CNES/argos-demo-board/Public/Image/ARGOS DEMO N°2.png

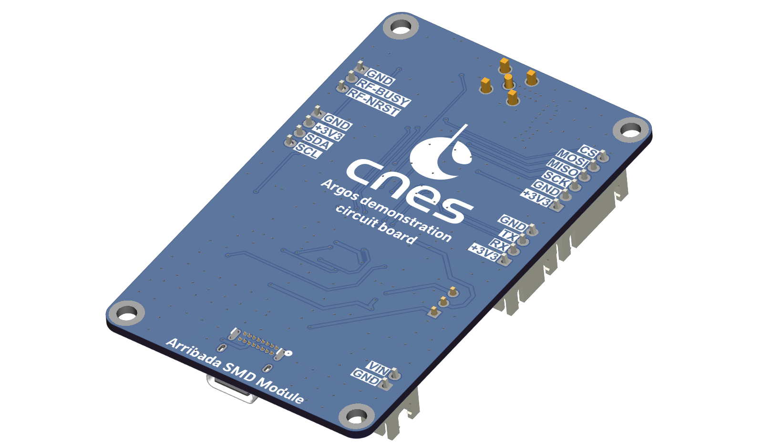
Public/Image/ARGOS DEMO N°2.png
