CNES/argos-demo-board/Public/Image/ARGOS DEMO N°7.png

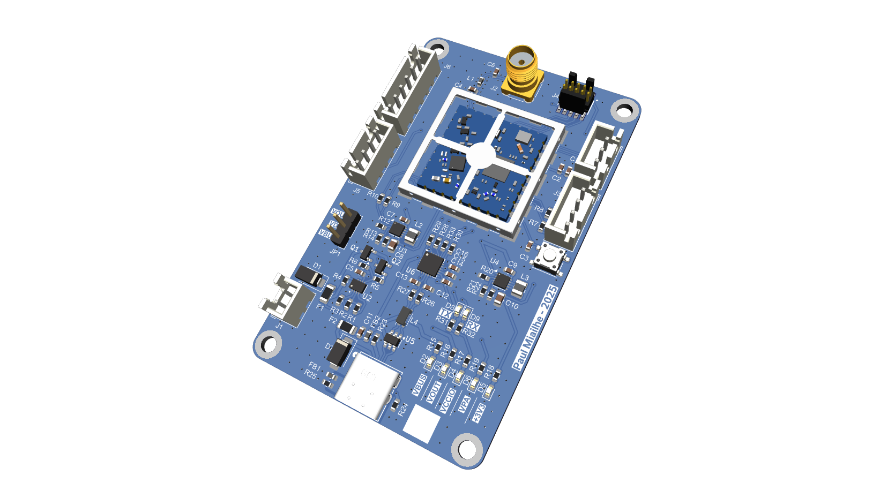
Public/Image/ARGOS DEMO N°7.png
