CNES/argos-demo-board/Public/Image/ARGOS DEMO N°11.png

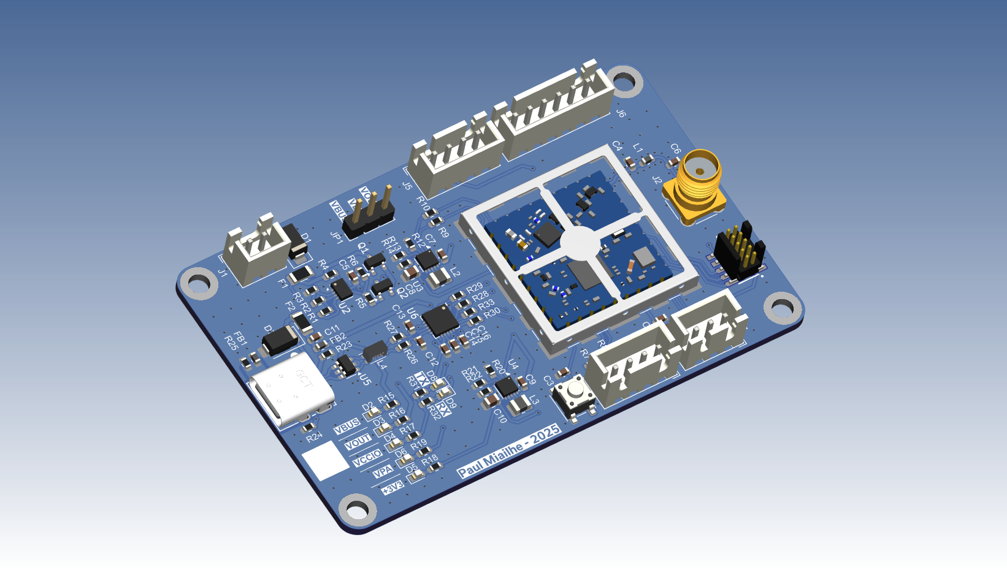
Public/Image/ARGOS DEMO N°11.png
