CNES/argos-demo-board/Public/Image/ARGOS DEMO N°12.png

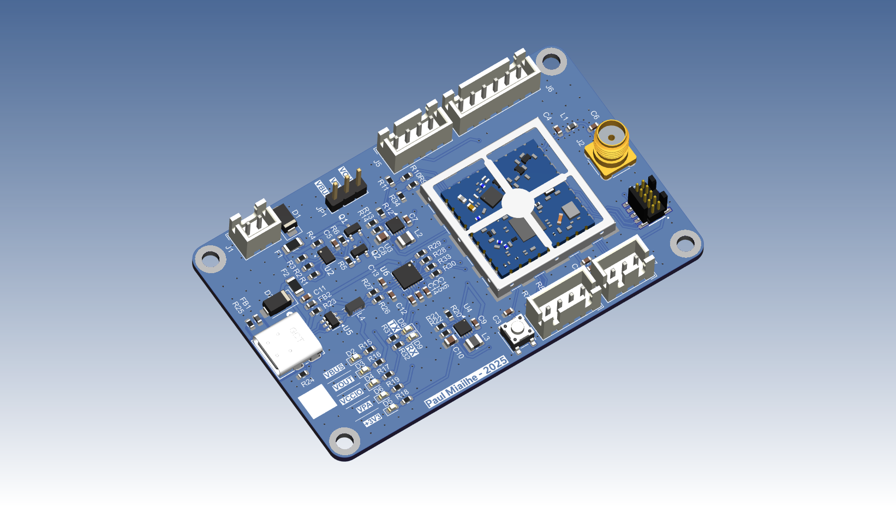
Public/Image/ARGOS DEMO N°12.png
