CNES/argos-demo-board/Public/Image/ARGOS DEMO N°14.png

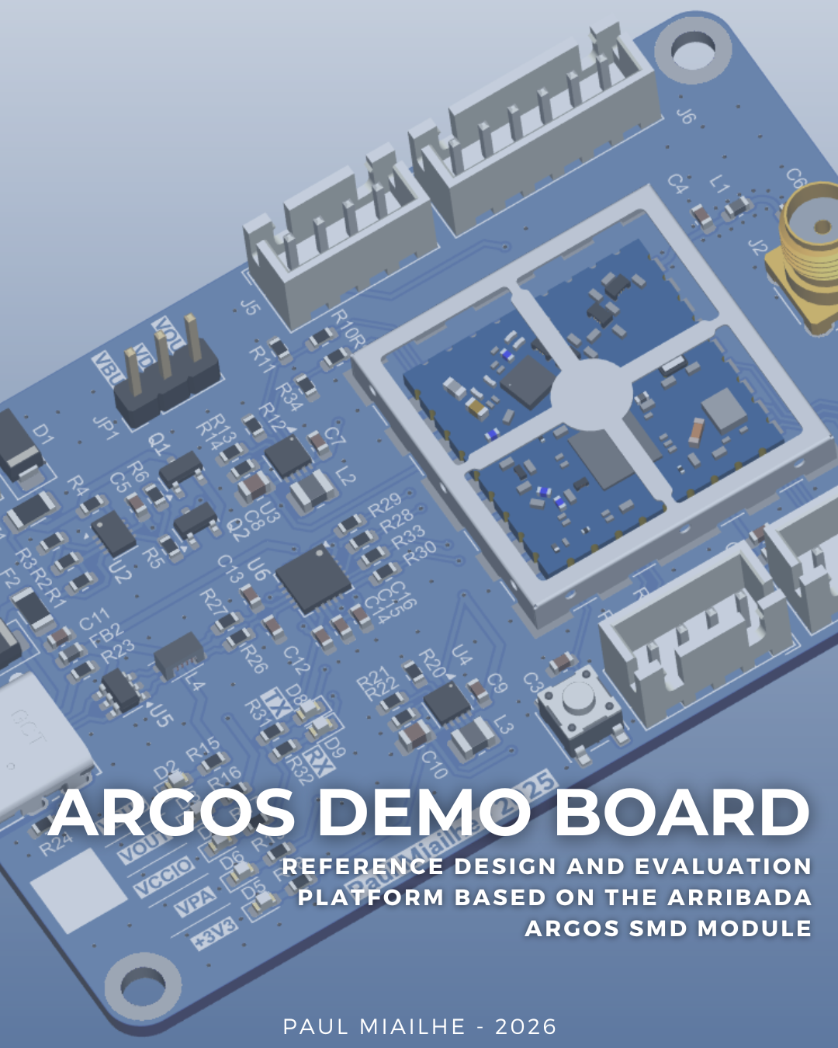
Public/Image/ARGOS DEMO N°14.png
