CNES/argos-demo-board/Librairies/3dmodels/FJ-15-D-02.00-4.stp

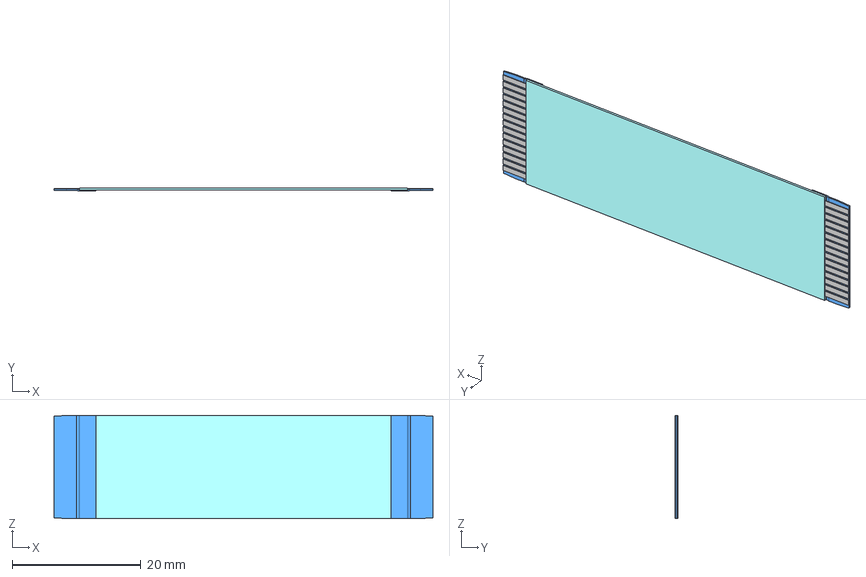
[picture p37: CAD file, 2026-01-29]
Librairies/3dmodels/FJ-15-D-02.00-4.stp
58.8 x 0.533 x 16.0 mm
FJ-15-D-02.00-4_cable
FJ-15-4_strip x 2
