CNES/argos-demo-board/Document/Test-VLDA4/Measurement037.png

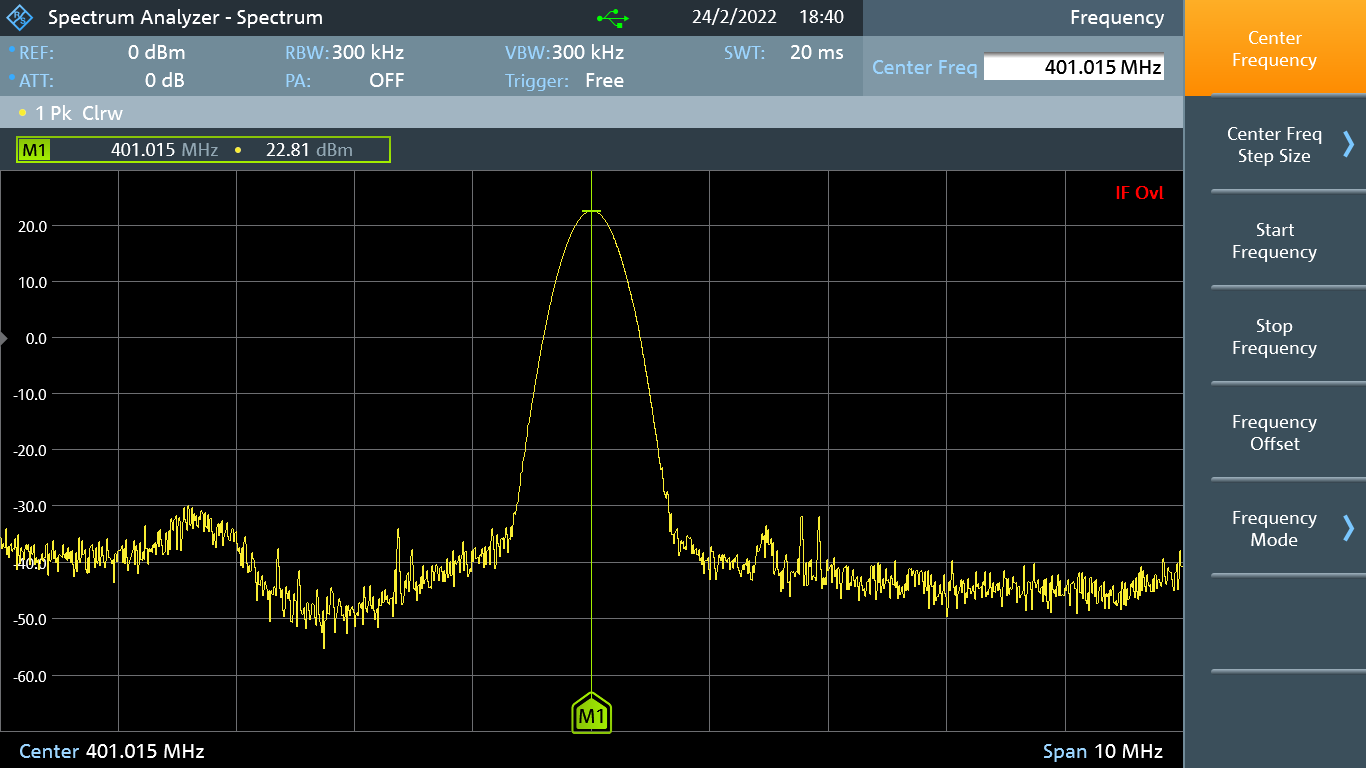
Document/Test-VLDA4/Measurement037.png
