CNES/argos-demo-board/Document/Test-VLDA4/Measurement038.png

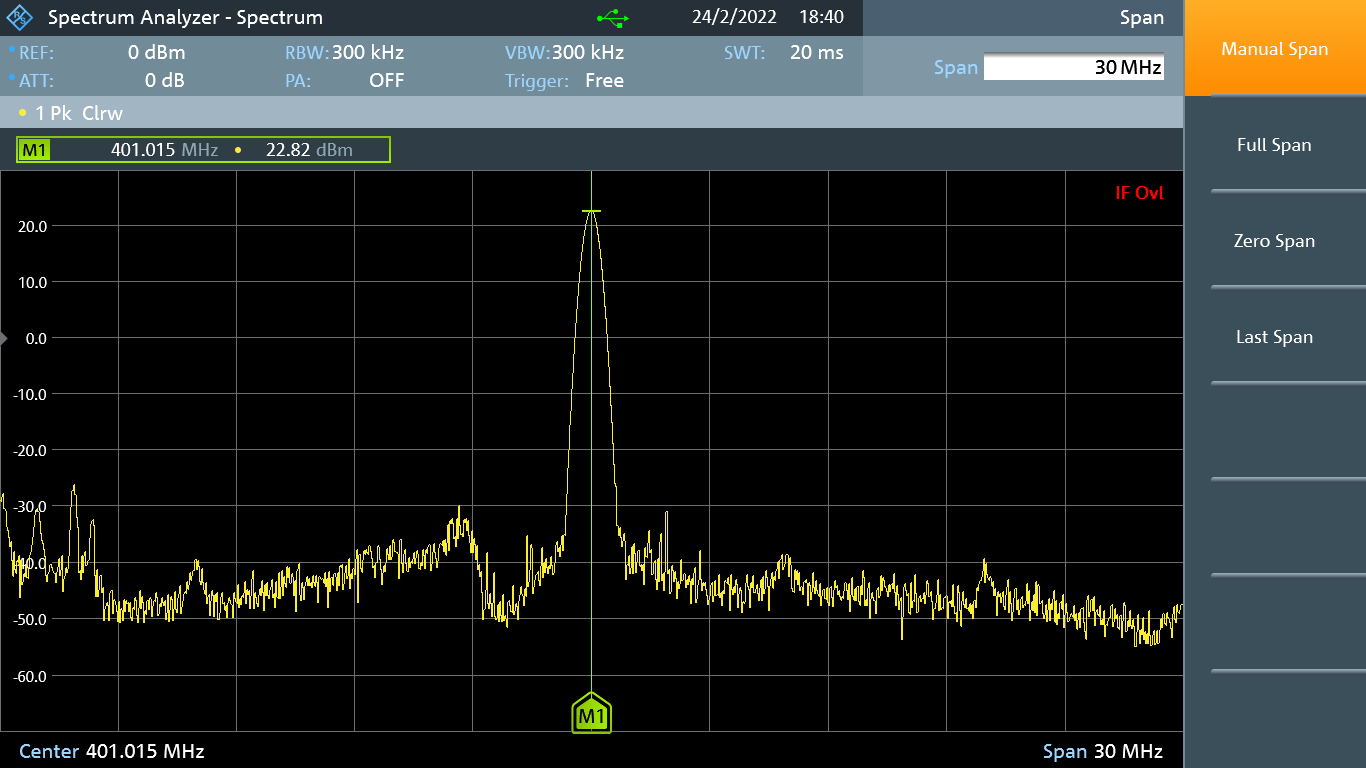
Document/Test-VLDA4/Measurement038.png
