CNES/argos-demo-board/Document/Test-VLDA4/Measurement040.png

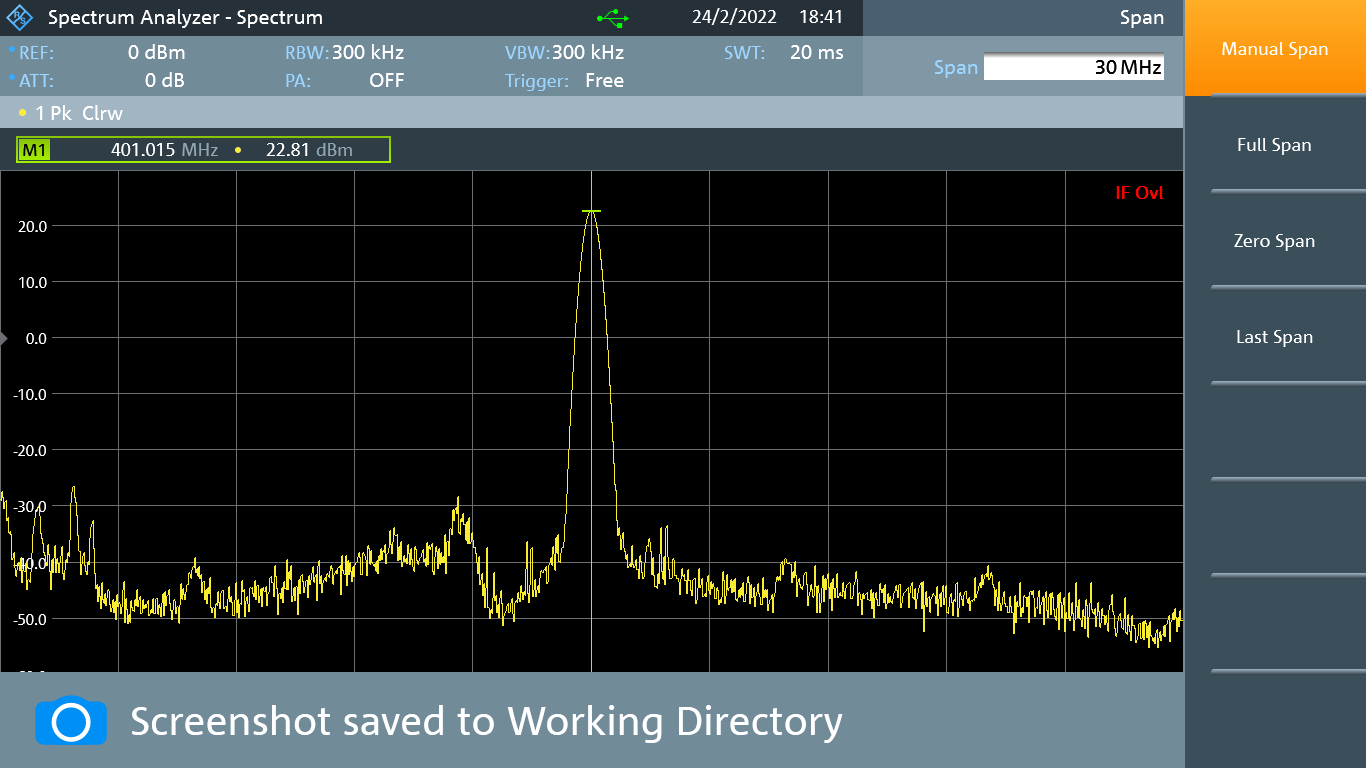
Document/Test-VLDA4/Measurement040.png
